anjrew/Autonomous-Nerf-Turret/components/camera_vision/data/musk.jpeg

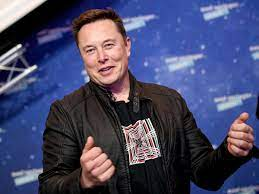
components/camera_vision/data/musk.jpeg
